EdoGitMira/ABB_RobotStudio_triennale/data/Cella-Robotizzata.png

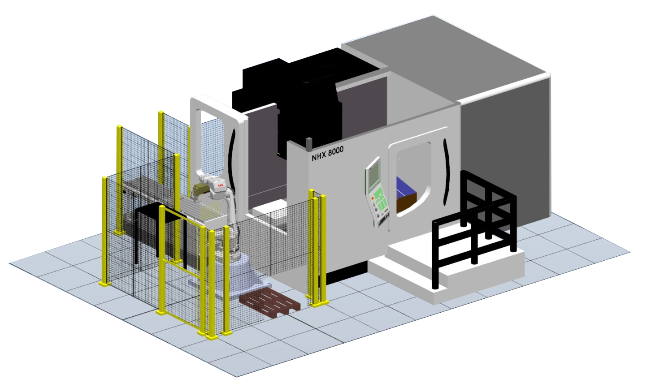
data/Cella-Robotizzata.png
