EdoGitMira/ABB_RobotStudio_triennale/data/foto/render1.png

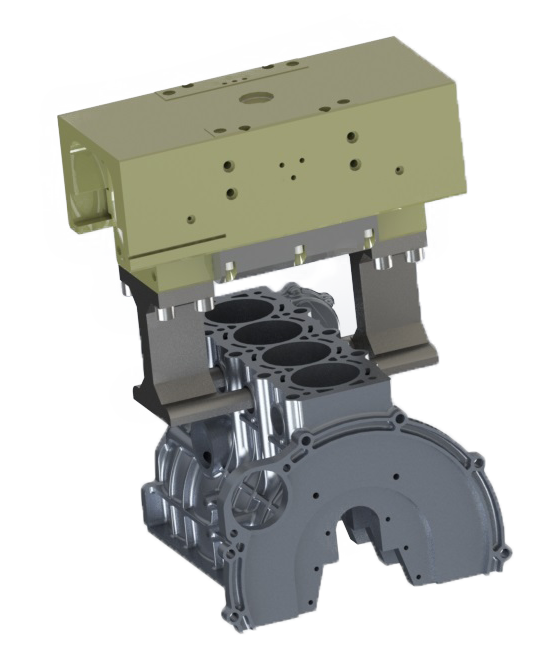
data/foto/render1.png
