EdoGitMira/ABB_RobotStudio_triennale/data/foto/render2.png

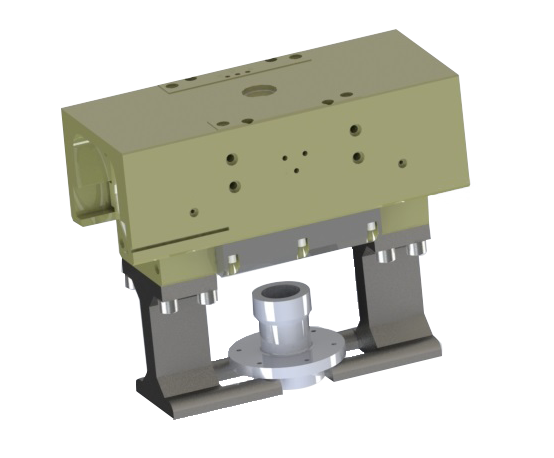
data/foto/render2.png
