EdoGitMira/ABB_RobotStudio_triennale/data/foto/stazione.jpg

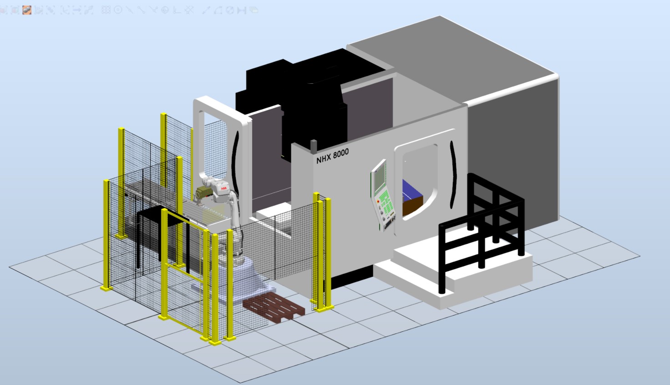
data/foto/stazione.jpg
