EdoGitMira/ABB_RobotStudio_triennale/data/foto/stazione_alto.jpg

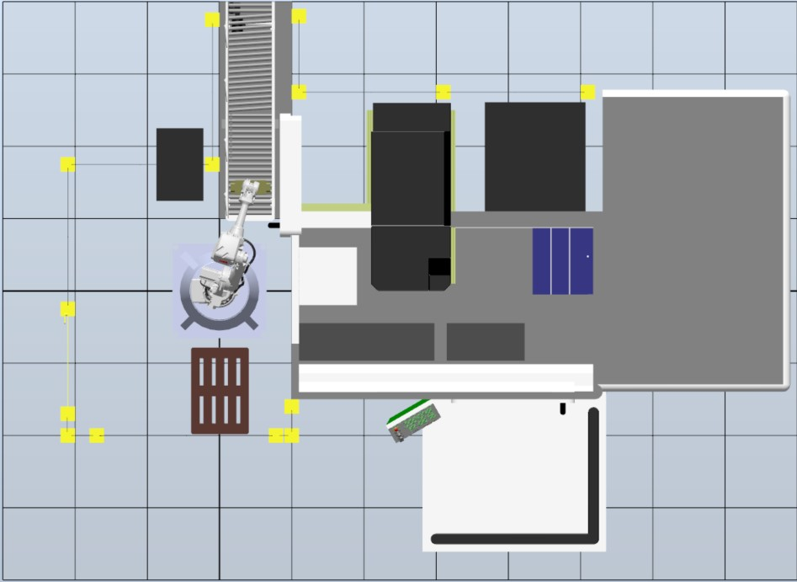
data/foto/stazione_alto.jpg
