EdoGitMira/ABB_RobotStudio_triennale/data/foto/stazione_davanti.jpg

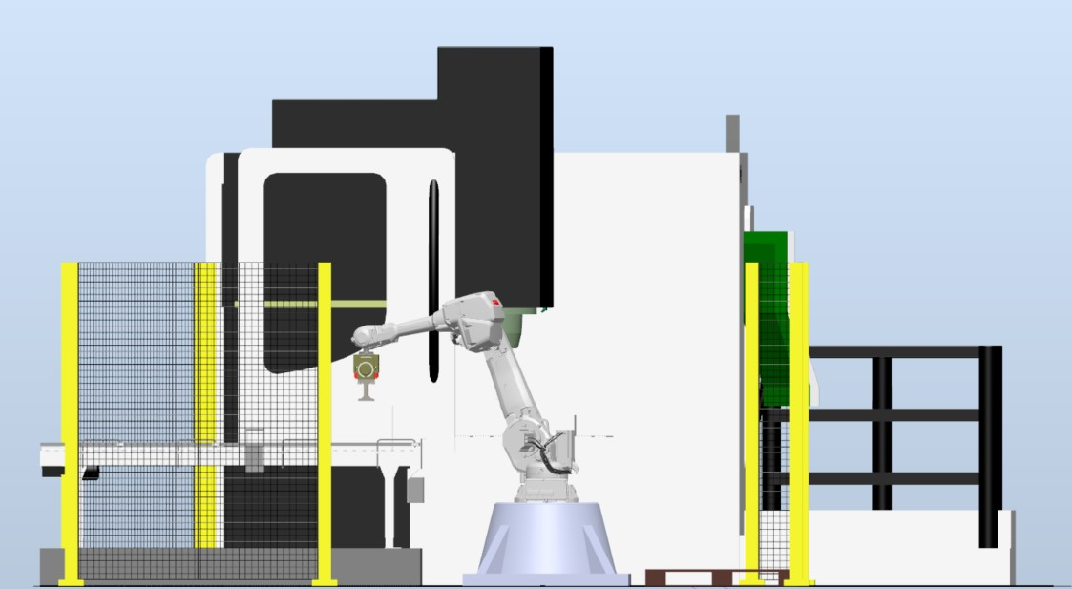
data/foto/stazione_davanti.jpg
