EdoGitMira/ABB_RobotStudio_triennale/data/foto/stazione_lato.jpg

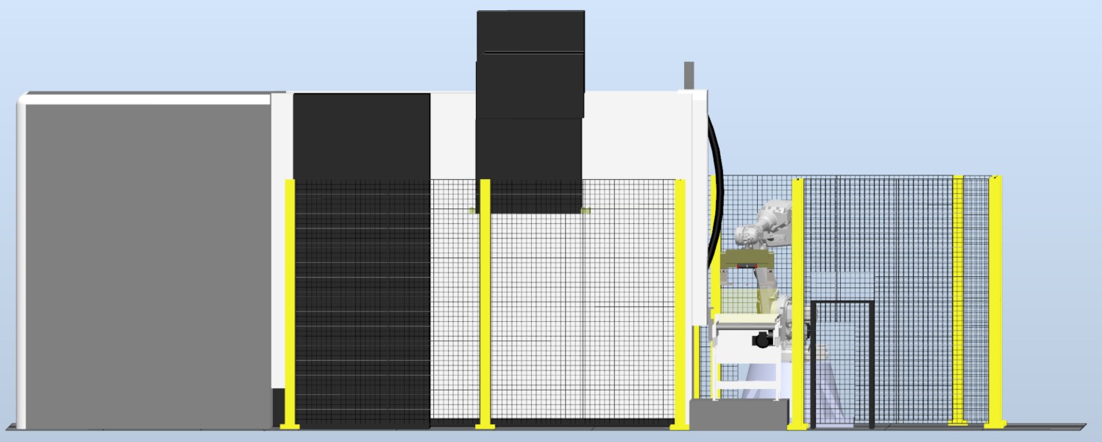
data/foto/stazione_lato.jpg
