EdoGitMira/ABB_RobotStudio_triennale/data/IRB4600.png

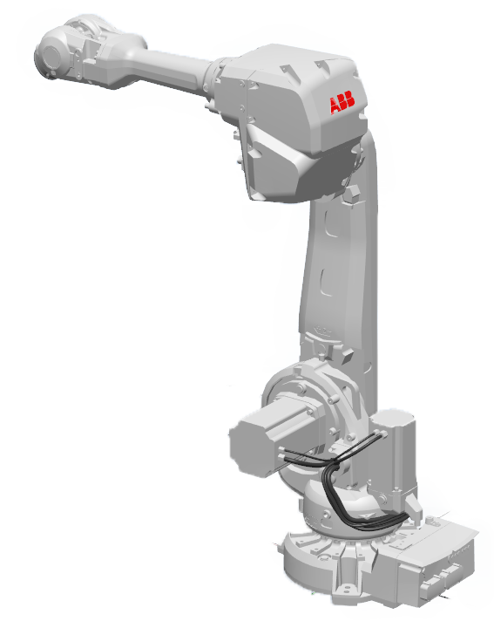
data/IRB4600.png
