EdoGitMira/ABB_RobotStudio_triennale/data/Pallet.png

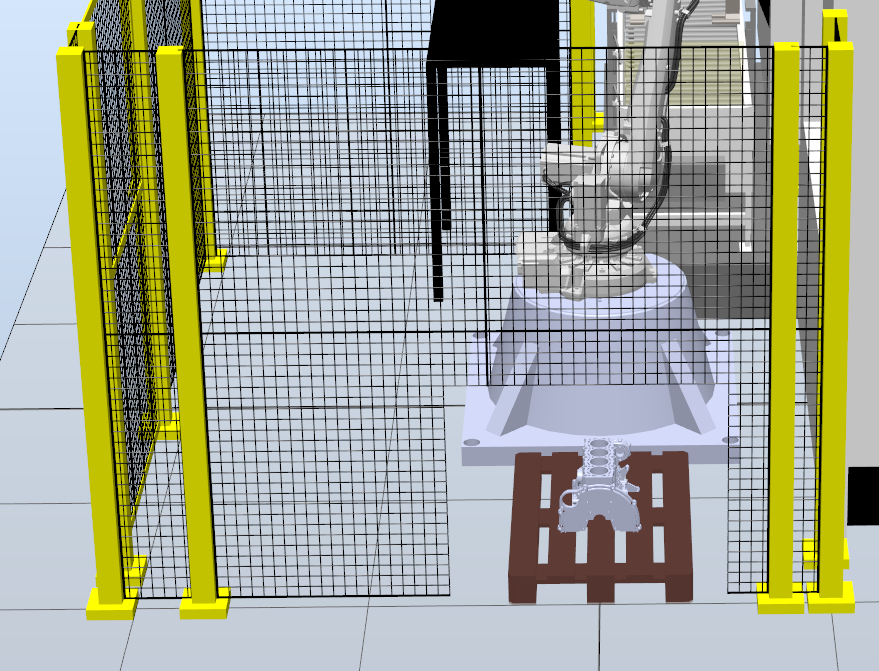
data/Pallet.png
