EdoGitMira/ABB_RobotStudio_triennale/data/SchermataIniziale2.png

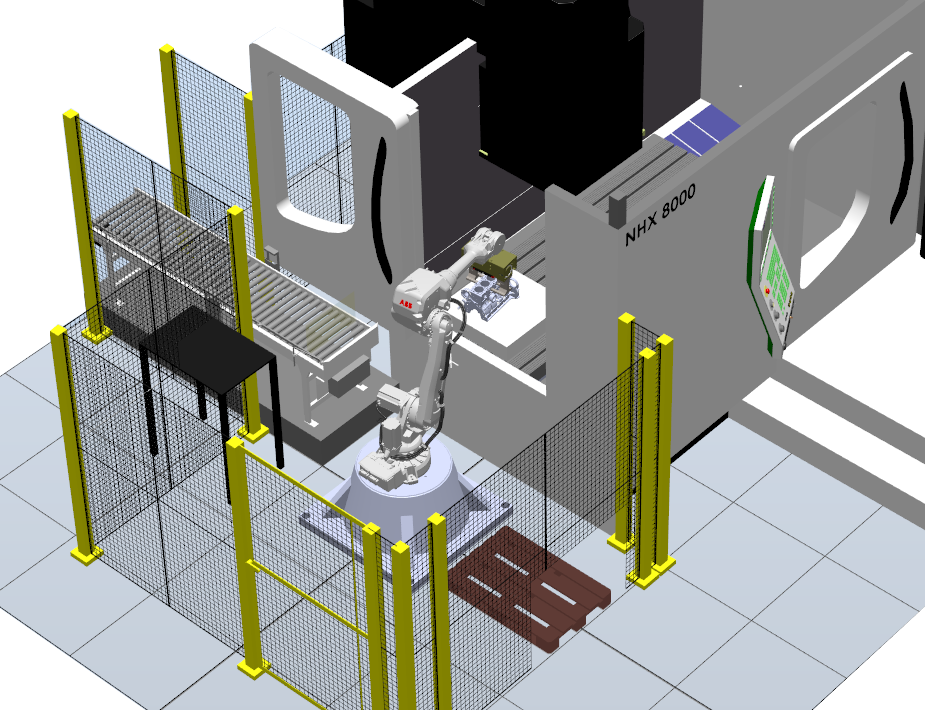
data/SchermataIniziale2.png
