EdoGitMira/ABB_RobotStudio_triennale/data/SchermataIniziale3.png

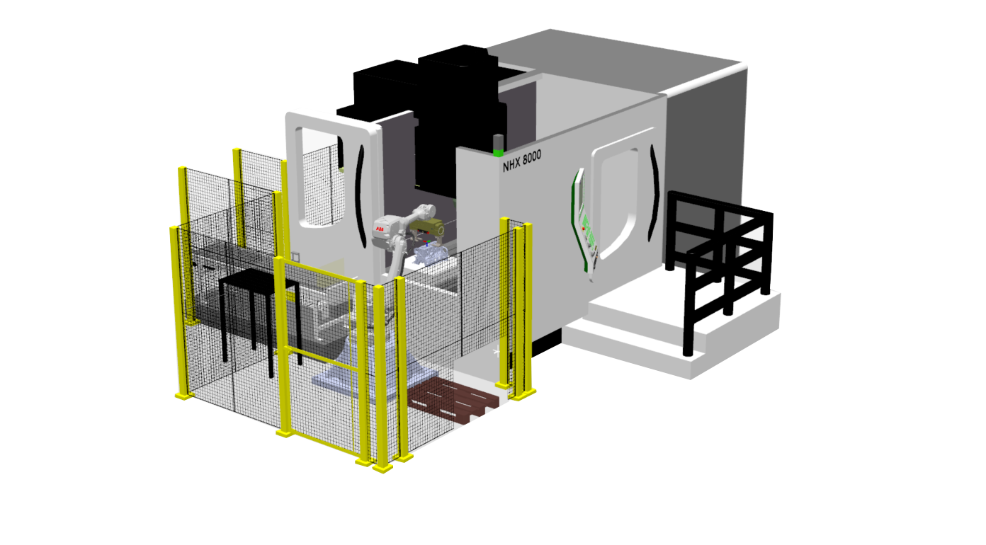
data/SchermataIniziale3.png
