EdoGitMira/ABB_RobotStudio_triennale/data/SchermataIniziale.png

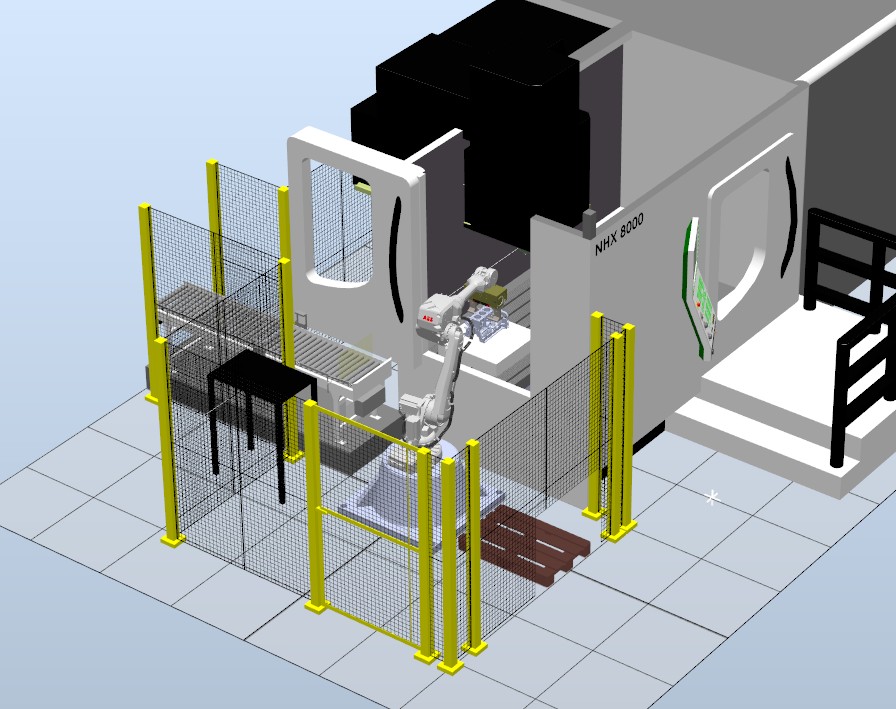
data/SchermataIniziale.png
