EdoGitMira/ABB_RobotStudio_triennale/disegni_solidworks/XSR201_nonlavorato.SLDPRT

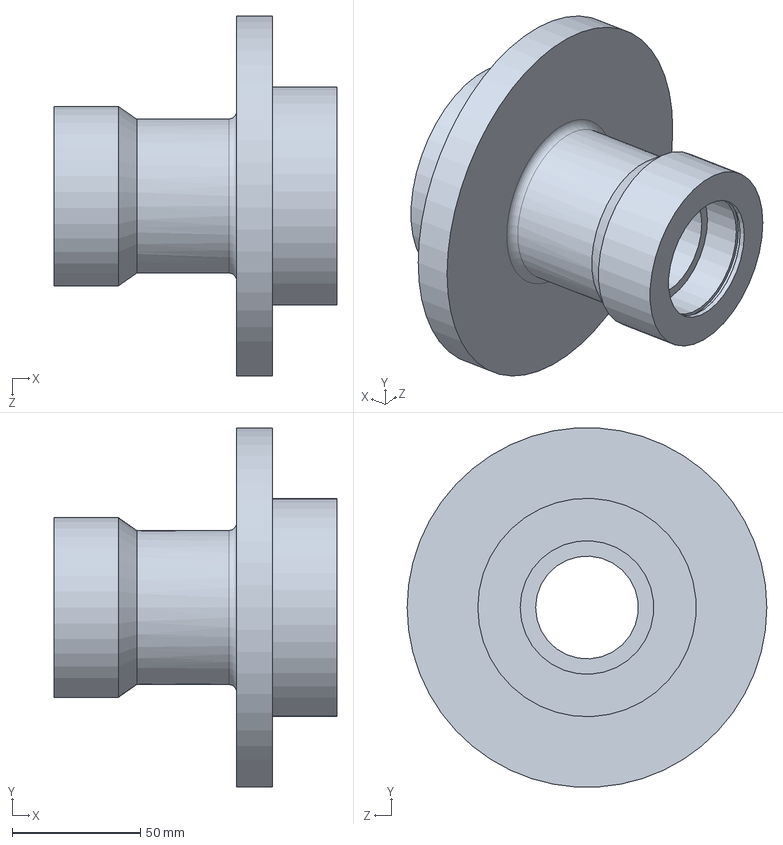
[picture p47: CAD file, 2022-12-22]
disegni_solidworks/XSR201_nonlavorato.SLDPRT
110.0 x 139.7 x 140.0 mm
