EdoGitMira/ABB_RobotStudio_triennale/disegni_solidworks/palo_barriera.SLDPRT

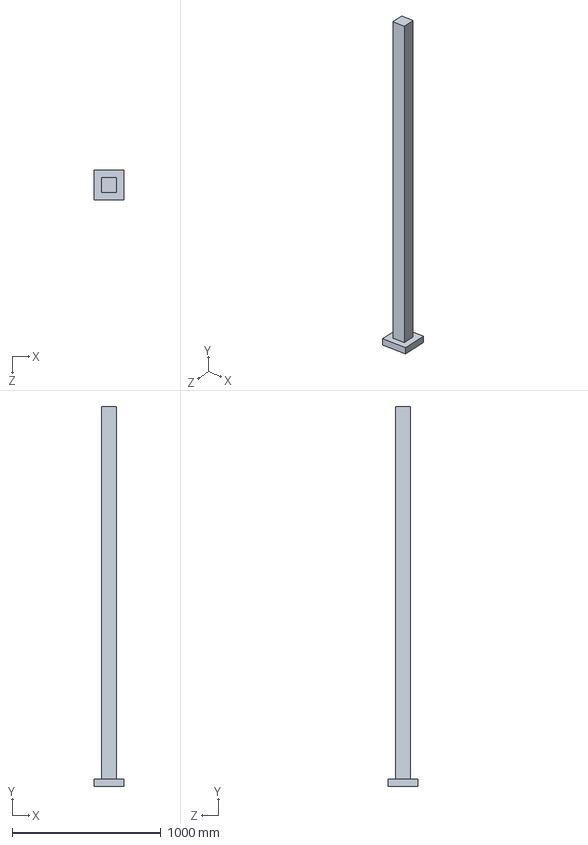
[picture p48: CAD file, 2022-12-22]
disegni_solidworks/palo_barriera.SLDPRT
200.0 x 2555.0 x 200.0 mm
