EdoGitMira/ABB_RobotStudio_triennale/disegni_solidworks/rete_1m.SLDPRT

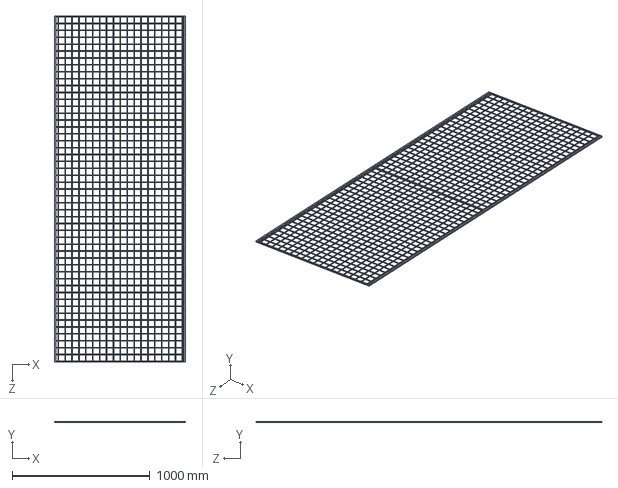
[picture p49: CAD file, 2022-12-22]
disegni_solidworks/rete_1m.SLDPRT
950.0 x 10.0 x 2507.5 mm
