EdoGitMira/ABB_RobotStudio_triennale/disegni_solidworks/rete_porta.SLDPRT

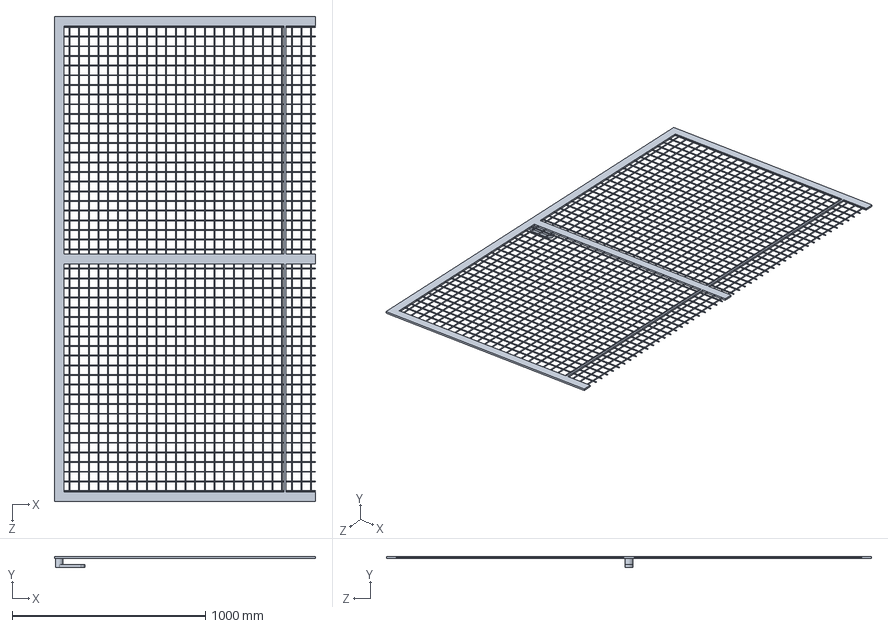
[picture p50: CAD file, 2022-12-22]
disegni_solidworks/rete_porta.SLDPRT
1350.0 x 55.0 x 2507.5 mm
