EdoGitMira/ABB_RobotStudio_triennale/disegni_solidworks/Parte1^bariera_1m.SLDPRT

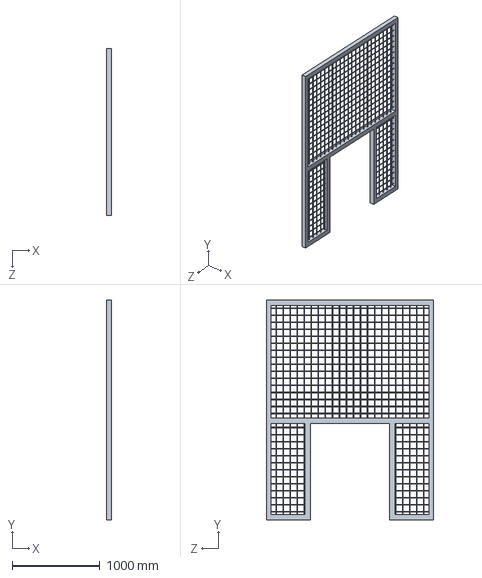
[picture p51: CAD file, 2022-12-22]
disegni_solidworks/Parte1^bariera_1m.SLDPRT
60.0 x 2505.0 x 1900.0 mm
