EdoGitMira/ABB_RobotStudio_triennale/disegni_solidworks/rete1m_c.SLDPRT

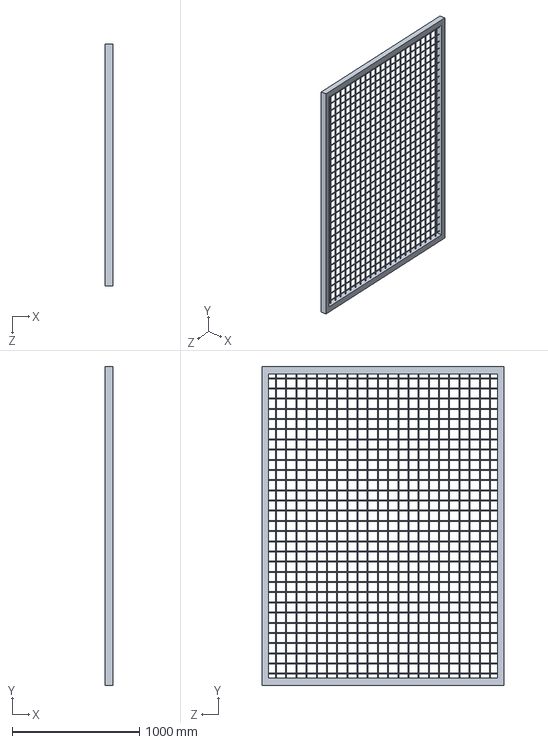
[picture p52: CAD file, 2022-12-22]
disegni_solidworks/rete1m_c.SLDPRT
60.0 x 2505.0 x 1900.0 mm
