EdoGitMira/ABB_RobotStudio_triennale/disegni_solidworks/rete200.SLDPRT

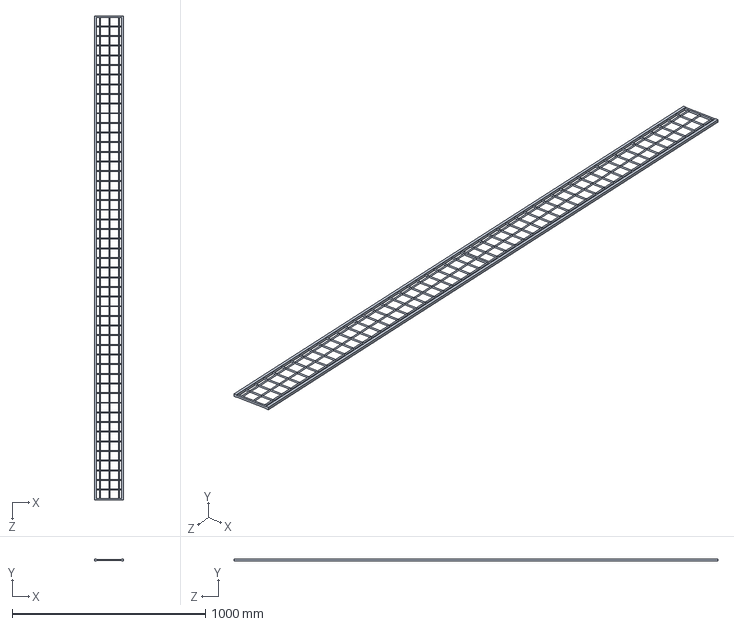
[picture p53: CAD file, 2022-12-22]
disegni_solidworks/rete200.SLDPRT
150.0 x 10.0 x 2507.5 mm
