EdoGitMira/ABB_RobotStudio_triennale/disegni_solidworks/ringhiera.SLDPRT

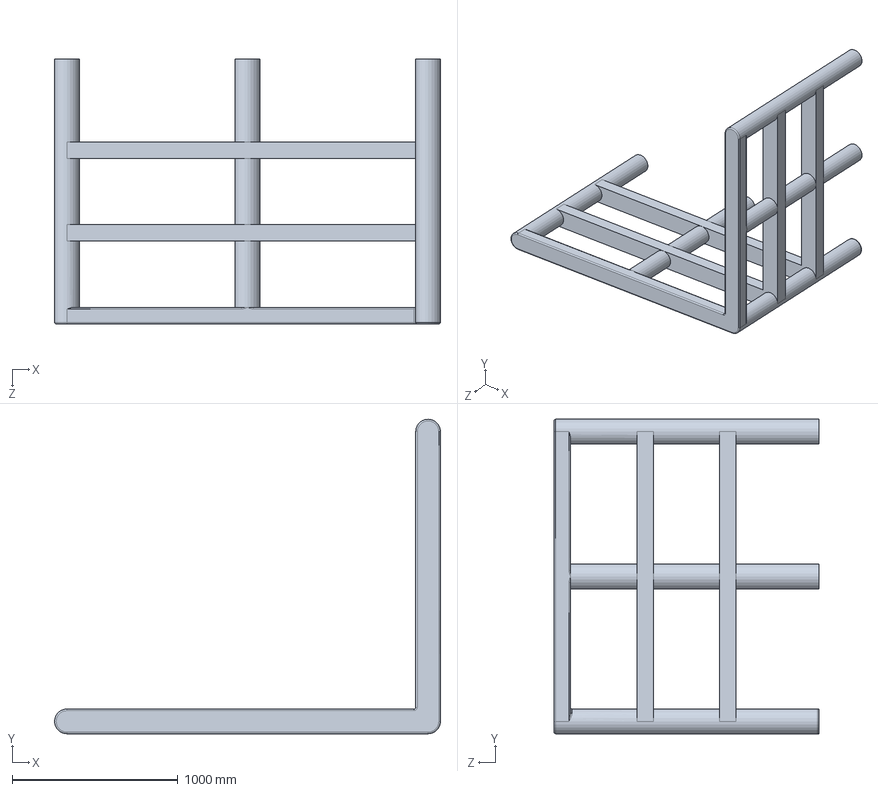
[picture p54: CAD file, 2022-12-22]
disegni_solidworks/ringhiera.SLDPRT
2330.3 x 1899.1 x 1600.0 mm
